lzambella/TinyBoard/TinyBoard/keymap.c

/*
Copyright 2012,2013 Jun Wako <wakojun@gmail.com>

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
You should have received a copy of the GNU General Public License
along with this program.  If not, see <http://www.gnu.org/licenses/>.
*/
#include <stdint.h>
#include <stdbool.h>
#include "keycode.h"
#include "action.h"
#include "action_macro.h"
#include "report.h"
#include "host.h"
#include "print.h"
#include "debug.h"
#include "keymap.h"

#define KEYMAP( \
    K00, K01, K02, K03, K04, K05, K06, K07, K08, K09, K0A, K0B, \
    K10, K11, K12, K13, K14, K15, K16, K17, K18, K19, K1A, K1B, \
    K20, K21, K22, K23, K24, K25, K26, K27, K28, K29, K2A, K2B, \
    K30, K31, K32, K33, K34, K35, K36, K37, K38, K39, K3A, K3B \
) { \
    { KC_##K00, KC_##K01, KC_##K02, KC_##K03, KC_##K04, KC_##K05, KC_##K06, KC_##K07, KC_##K08, KC_##K09, KC_##K0A, KC_##K0B}, \
    { KC_##K10, KC_##K11, KC_##K12, KC_##K13, KC_##K14, KC_##K15, KC_##K16, KC_##K17, KC_##K18, KC_##K19, KC_##K1A, KC_##K1B}, \
    { KC_##K20, KC_##K21, KC_##K22, KC_##K23, KC_##K24, KC_##K25, KC_##K26, KC_##K27, KC_##K28, KC_##K29, KC_##K2A, KC_##K2B}, \
    { KC_##K30, KC_##K31, KC_##K32, KC_##K33, KC_##K34, KC_##K35, KC_##K36, KC_##K37, KC_##K38, KC_##K39, KC_##K3A, KC_##K3B}  \
}

const uint8_t PROGMEM keymaps[][MATRIX_ROWS][MATRIX_COLS] = {
    [0] = KEYMAP(
        ESC,    Q,    W,    E,   R,      T,    Y,     U,      I,     O,    P,      BSLASH, \
        TAB,    A,    S,    D,   F,      G,    H,     J,      K,     L,    QUOTE, ENTER,  \
        LSHIFT, Z,    X,    C,   V,      B,    N,     M,      COMMA, DOT,  SLASH,  RSHIFT, \
        LCTRL,  LGUI, LALT, FN0, SPACE,  NO,   SPACE, BSPACE, FN1,   RALT,  RGUI,  RCTRL
    ),
    [1] = KEYMAP(
        GRAVE,    1,    2,    3,   4,      5,    6,     7,      8,     9,    0,      MINUS, \
        NO,    NO,    NO,    NO,   NO,      NO,    HOME,     END,      LBRACKET,     RBRACKET, SCOLON, ENTER,  \
        LSHIFT,    NO,    NO,    NO,   NO,      NO,    PGUP,     PGDOWN,      NO, NO,  NO,  RSHIFT, \
        LCTRL,  LGUI, LALT, FN0, SPACE,  NO,   SPACE, EQUAL, FN1,   RALT,  RGUI,  RCTRL
    ),
    [2]= KEYMAP(
        DELETE,    F1,    F2,    F3,   F4,      F5,    F6,     F7,      F8,     F9,    F10,      F11, \
        NO,    NO,    NO,    NO,   NO,      NO,    NO,     NO,      NO,     UP, NO, ENTER,  \
        LSHIFT,    NO,    NO,    NO,   NO,      NO,    PGUP,     PGDOWN,      LEFT, DOWN,  RIGHT,  RSHIFT, \
        LCTRL,  LGUI, LALT, FN0, SPACE,  NO,   SPACE, F12, FN1,   RALT,  RGUI,  RCTRL
    ),
};

/*
 * Fn action definition
 */
const action_t PROGMEM fn_actions[] = {
    [0]  = ACTION_LAYER_MOMENTARY(1),
    [1]  = ACTION_LAYER_MOMENTARY(2)
};
